cron-eu/arduino-siedle-gateway/hardware/arduino-doorbell/arduino-doorbell.sch

## EAGLE design hardware/arduino-doorbell/arduino-doorbell.sch (2020-01-23)

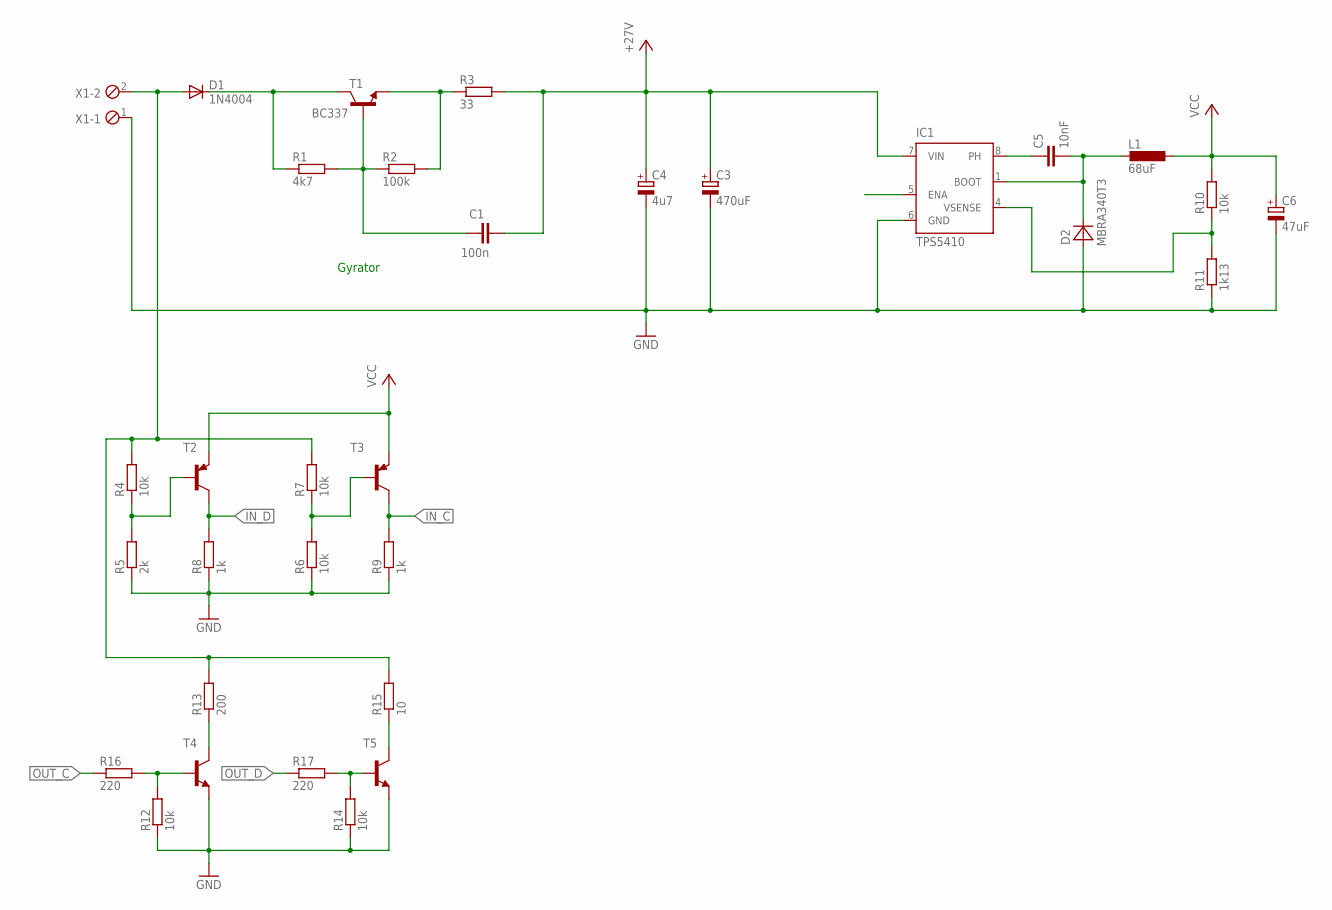
[picture p3: schematic arduino-doorbell.sch]

Parts:
C1: 100n; C050-025X075
C3: 470uF; E3,5-10
C4: 4u7; E3,5-10
C5: 10nF; C025-030X050
C6: 47uF; E3,5-10
D1: 1N4004; DO41-10
D2: MBRA340T3; SMA
IC1: TPS5410; D_R-PDSO-G08
L1: 68uF; DO3316P
R1: 4k7; 0204/5
R2: 100k; 0204/5
R3: 33; 0204/5
R4, R6, R7, R10, R12, R14: 10k; 0204/5
R5: 2k; 0204/5
R8, R9: 1k; 0204/5
R11: 1k13; 0204/5
R13: 200; 0204/5
R15: 10; 0204/5
R16, R17: 220; 0204/5
T1: BC337; TO92
T2, T3: -PNP-TO92; TO92
T4, T5: -NPN-SOT23-EBC; SOT23-EBC
X1: MPT2; 2POL254

Connections:
+27V: C1.2, C3.+, C4.+, IC1.7 (VIN), R3.2
GND: C3.-, C4.-, C6.-, D2.A, IC1.6 (GND), R5.1, R6.1, R8.1, R9.1, R11.1, R12.1, R14.1, T4.E, T5.E, X1.1
IN_C: R9.2, T3.3 (C)
IN_D: R8.2, T2.3 (C)
unnamed: C1.1, R1.2, R2.1, T1.2 (B)
unnamed: R2.2, R3.1, T1.1 (E)
unnamed: R4.1, R5.2, T2.2 (B)
unnamed: D1.C, R1.1, T1.3 (C)
unnamed: C5.1, IC1.8 (PH)
unnamed: R6.2, R7.1, T3.2 (B)
unnamed: C5.2, D2.C, IC1.1 (BOOT), L1.1
unnamed: IC1.4 (VSENSE), R10.1, R11.2
unnamed: R12.2, R16.2, T4.B
unnamed: R13.1, T4.C
unnamed: R14.2, R17.2, T5.B
unnamed: R15.1, T5.C
OUT_C: R16.1
OUT_D: R17.1
VCC: C6.+, L1.2, R10.2, T2.1 (E), T3.1 (E)
X1: D1.A, R4.2, R7.2, R13.2, R15.2, X1.2

Notes on the sheet:
Gyrator
