cron-eu/arduino-siedle-gateway/hardware/arduino-doorbell/experimental.sch

## EAGLE design hardware/arduino-doorbell/experimental.sch (2020-02-01)

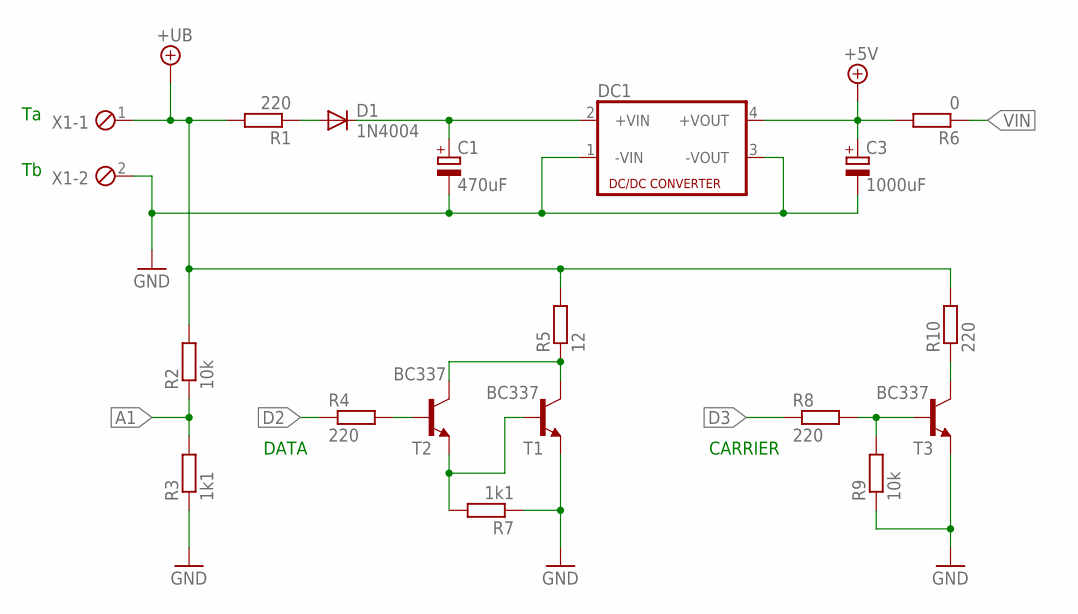
[picture p4: schematic experimental.sch]

Parts:
C1: 470uF; EB20D
C3: 1000uF; EB20D
D1: 1N4004; DO41-10
DC1: NME
R1, R4, R8, R10: 220; 0204/7
R2, R9: 10k; 0204/7
R3, R7: 1k1; 0204/7
R5: 12; 0204/7
R6: 0; 0204/7
T1, T2, T3: BC337; TO92
X1: MPT2; 2POL254

Connections:
+5V: C3.+, DC1.4 (+VOUT), R6.2
+UB: R1.2, R2.2, R5.2, R10.2, X1.1
A1: R2.1, R3.2
D2: R4.1
D3: R8.1
GND: C1.-, C3.-, DC1.1 (-VIN), DC1.3 (-VOUT), R3.1, R7.1, R9.1, T1.1 (E), T3.1 (E), X1.2
unnamed: C1.+, D1.C, DC1.2 (+VIN)
unnamed: D1.A, R1.1
unnamed: R4.2, T2.2 (B)
unnamed: R5.1, T1.3 (C), T2.3 (C)
unnamed: R7.2, T1.2 (B), T2.1 (E)
unnamed: R8.2, R9.2, T3.2 (B)
unnamed: R10.1, T3.3 (C)
VIN: R6.1

Notes on the sheet:
DATA
CARRIER
