cron-eu/arduino-siedle-gateway/firmware/src/wifi-manager.cpp

//
// Created by Remus Lazar on 04.02.20.
//

#include "wifi-manager.h"

#include <Arduino.h>
#ifdef ARDUINO_ARCH_SAMD
#include <WiFiNINA.h>
#elif defined(ESP8266)
#include <ESP8266WiFi.h>
#ifdef MDNS_HOSTNAME
#include <ESP8266mDNS.h>
#endif
#endif

#include <wifi_client_secrets.h>
#include "settings.h"

void WiFiManagerClass::loop() {
    if (millis() - connectionCheckMillis > 250) { // check connection status periodically
        connectionCheckMillis = millis();

        auto status = WiFi.status();
        if ( (status == WL_CONNECTED) != connected) {
            connected = (status == WL_CONNECTED);
            if (connected) {
                printWifiStatus();
                #ifdef MDNS_HOSTNAME
                DEBUG_PRINTLN(String(F("mDNS service started for hostname: ")) + F(MDNS_HOSTNAME));
                MDNS.begin(F(MDNS_HOSTNAME));
                #endif
            }
        }

        #ifdef ARDUINO_ARCH_SAMD
        if (!connected && millis() - reconnectMillis > 5000) { // reconnect every 5 seconds
            connect();
            reconnectMillis = millis();
        }
        #endif
    }
    #ifdef MDNS_HOSTNAME
    MDNS.update();
    #endif
}

void WiFiManagerClass::begin() {
    #ifdef ARDUINO_ARCH_SAMD
    reconnectMillis = 0;
    #endif
    connectionCheckMillis = 0;
    wifiReconnects = 0;

#ifdef ARDUINO_ARCH_SAMD
#ifdef USE_WIFI_LOW_POWER
    WiFi.lowPowerMode();
#endif
#endif

    connect();
}

void WiFiManagerClass::connect() {
    String ssid = F(SECRET_SSID);
    String pass = F(SECRET_PASS);
    DEBUG_PRINT(String(F("Connecting to WiFi Network '")) + ssid + "' .. ");
    #ifdef ARDUINO_ARCH_SAMD
    WiFi.begin(SECRET_SSID, SECRET_PASS);
    #elif defined(ESP8266)
    WiFi.begin(ssid, pass); // this will run async

    #endif
    }

void WiFiManagerClass::printWifiStatus() {
    // print the SSID of the network you're attached to:
    DEBUG_PRINTLN("done!");

    #ifdef ARDUINO_ARCH_SAMD
    auto localIP = WiFi.localIP();
    #elif defined(ESP8266)
    auto localIP = WiFi.localIP().toString();
    #endif

    // print ip and rssi of the current link
    DEBUG_PRINTLN(String(F("Local IP: ")) + localIP
                + F(", signal strength (RSSI): ") + WiFi.RSSI() + F(" dBm."));
}

WiFiManagerClass WiFiManager;
