cron-eu/arduino-siedle-gateway/firmware/src/web-ui.h

//
// Created by Remus Lazar on 04.02.20.
//

#ifndef FIRMWARE_WEB_UI_H
#define FIRMWARE_WEB_UI_H

#include <Arduino.h>
#ifdef ARDUINO_ARCH_SAMD
#include <MemoryUtils.h>
#include <RTCZero.h>
#endif

#include "main_profiling.h"

/**
 * Determine the boot time of the system
 *
 * @return number of seconds since the system has booted up
 */
unsigned long getUptime() {
    if (RTCSync.bootEpoch > 0) { return RTCSync.getEpoch() - RTCSync.bootEpoch; }
    // else, NTP not initialized
    return millis() / 1000;
}

void webUIHTMLHandler(Print *handler) {

    time_t time;

    handler->print("<h3>Device Status</h3>");

    handler->print("<dl><dt>Uptime</dt><dd>");

    auto uptime = getUptime();
    if (uptime > 24 * 3600) {
        handler->print((float)uptime / (24 * 3600), 1);
        handler->print(" days");
    } else if (uptime > 3600) {
        handler->print((float)uptime / 3600, 1);
        handler->print(" hr");
    } else {
        handler->print((float)uptime / 60, 0);
        handler->print(" min");
    }
    handler->print("</dd></dl>");


    handler->print("<dl><dt>WiFi</dt><dd>");

    handler->print("SSID: ");
    handler->print(WiFi.SSID());
    // print the received signal strength:
    long rssi = WiFi.RSSI();
    handler->print(", RSSI:");
    handler->print(rssi);
    handler->println(" dBm");
    handler->print("(");
    handler->print(WiFiManager.wifiReconnects);
    handler->println(")");

    handler->print("</dd></dl>");

    handler->print("<dl><dt>Free Memory</dt><dd>");
    #ifdef ARDUINO_ARCH_SAMD
    handler->println(freeMemory());
    #elif defined(ESP8266)
    handler->println(ESP.getFreeHeap());
    #endif
    handler->print("</dd></dl>");

    handler->print("<dl><dt>Date/Time (UTC)</dt><dd>");
    time = RTCSync.getEpoch();
    handler->println(ctime(&time));
    handler->print("</dd></dl>");

//    handler->print("<dl><dt>Siedle Bus IRQ Count</dt><dd>");
//    handler->println(SiedleService.siedleClient.irq_count);
//    handler->print("</dd></dl>");

#ifdef USE_MQTT
    handler->print("<dl><dt>MQTT Status (Reconnects)</dt><dd>");
    switch (MQTTService.state) {
        case mqtt_not_connected:
            handler->println("Not Connected");
            break;
        case mqtt_connected:
            handler->println("Connecting");
            break;
        case mqtt_connected_and_subscribed:
            handler->println("Ready");
            break;
    }
    handler->print("(");
    handler->print(MQTTService.mqttReconnects);
    handler->println(")");
    handler->println("</dd>");

    handler->println("<dt>MQTT Rx/Tx/Overruns Count</dt>");
    handler->print("<dd>");
    handler->print(MQTTService.rxCount);
    handler->print(" / ");
    handler->print(MQTTService.txCount);
    handler->print(" / ");
    handler->print(MQTTService.overruns);
    handler->println("</dd>");

#endif

    handler->print("<dl><dt>Siedle Bus Rx/Tx/Overruns Count</dt><dd>");
    handler->print(SiedleService.siedleClient.rxCount);
    handler->print(" / ");
    handler->print(SiedleService.siedleClient.txCount);
    handler->print(" / ");
    handler->print(SiedleService.overruns);
    handler->print("</dd></dl>");

    handler->println(
        String("<dl><dt>Mainloop max ms</dt><dd>") + max_main_loop_duration_ms + String("</dd></dl>")
    );

    handler->print("<h3>Data</h3><table><tr><th>Timestamp</th><th>Direction</th><th>Command</th></tr>");
    for (unsigned int i = 0; i < siedleRxTxLog.size(); i++) {
        auto entry = siedleRxTxLog[i];
        time = entry.log.timestamp;
        handler->print("");

        auto html = String("<tr><td>") + ctime(&time)
            + String("</td><td>") + (entry.direction == rx ? "&larr;" : "&rarr;")
            + String("</td><td><pre>")
            + String(entry.log.cmd, 16) + "</pre></td></tr>";

        handler->print(html);
    }

    handler->print("</table>");
}

#endif //FIRMWARE_WEB_UI_H
